Shine-Bright-Meow/meowCarrier/Resources/Images/PCB/PCB_Bottom.png

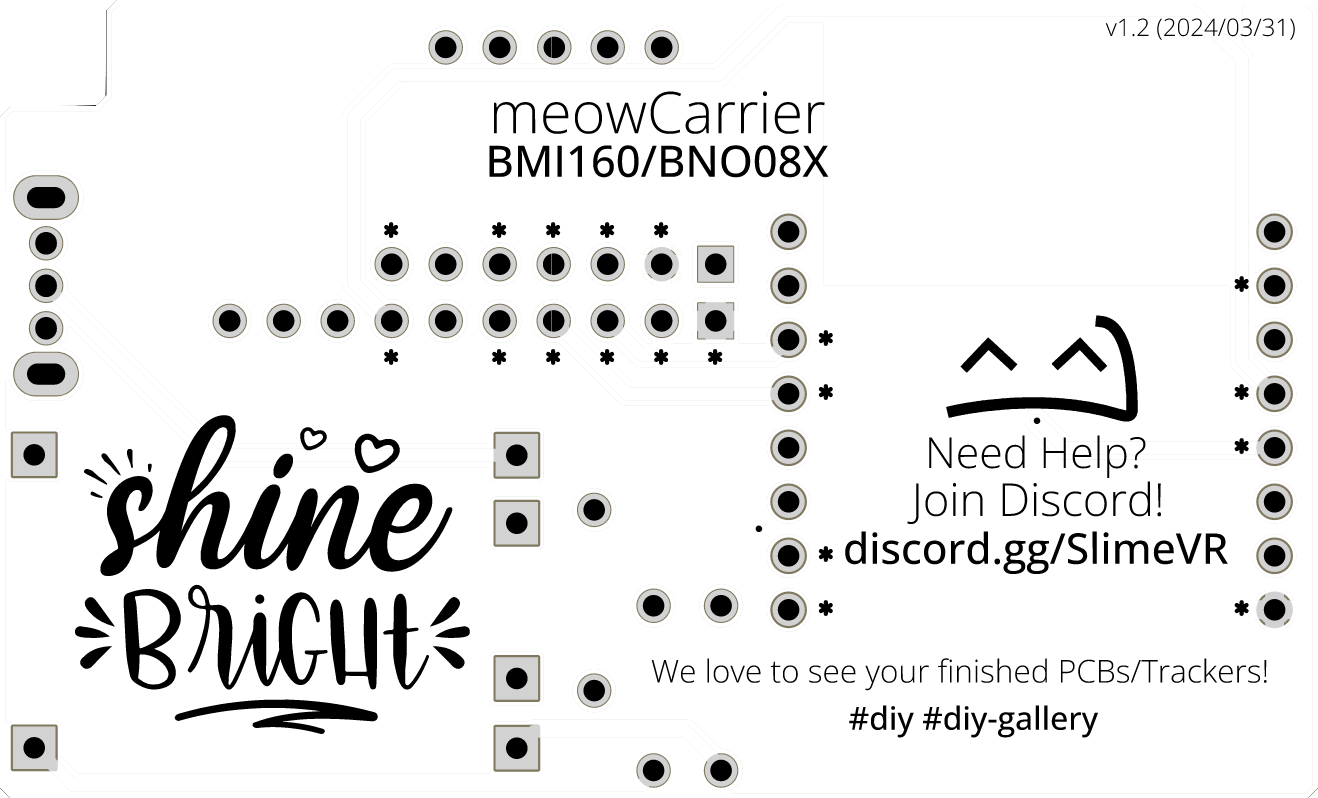
Resources/Images/PCB/PCB_Bottom.png
